daremus/tabletop_turn_timer/schematics/tabletop_game_timer_v1.kicad_sch

## KiCad design schematics/tabletop_game_timer_v1.kicad_sch (2026-09-04)

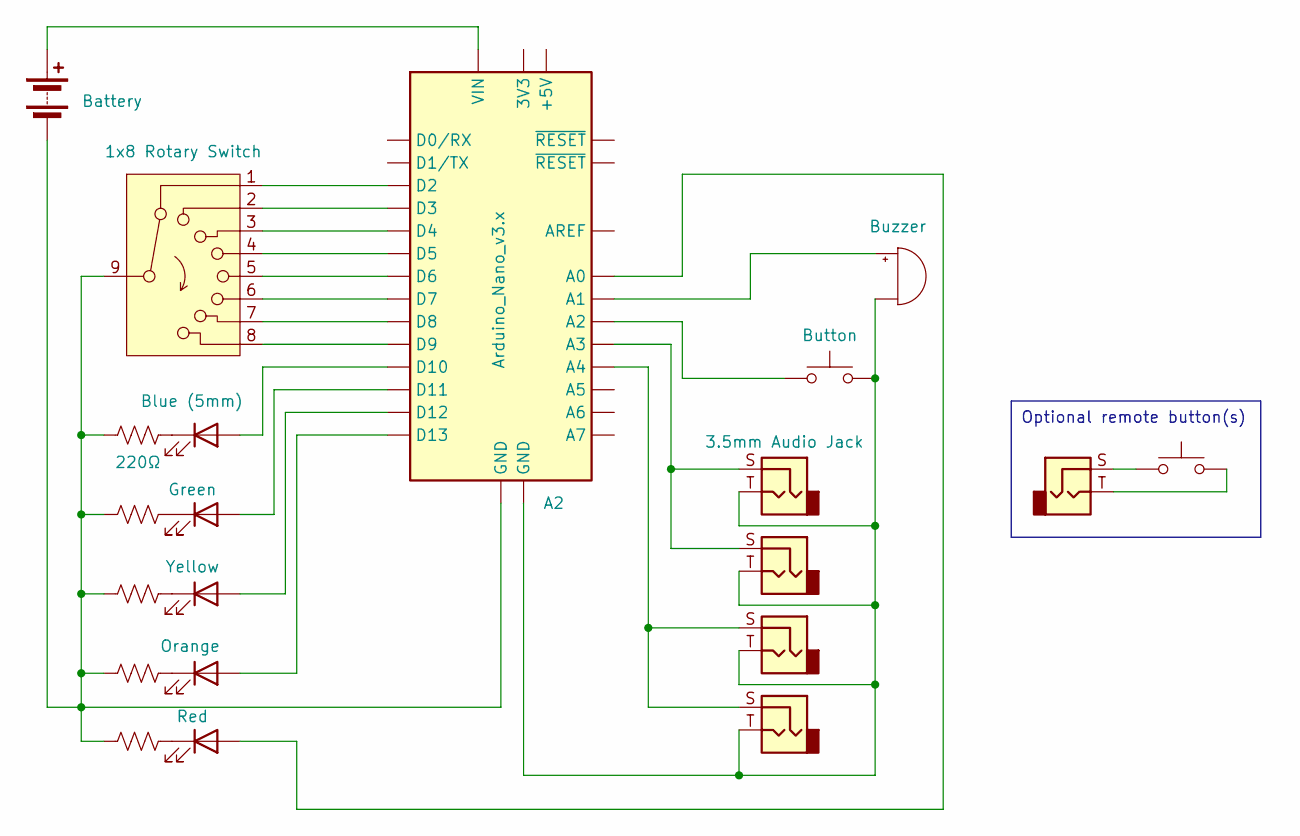
[picture p8: schematic tabletop_game_timer_v1.kicad_sch]

Parts:
220Ω, 220Ω1: R_US
A2: Arduino_Nano_v3.x; Arduino_Nano
BT1: Battery
BZ1: Buzzer
Blue: Blue (5mm)
Green: LED
J1, J2, J3, J4, J5: 3.5mm Audio Jack
Orange: LED
Red: LED
SW1: 1x8 Rotary Switch
SW2, SW3: Button
Yellow: LED

Connections:
unnamed: 220Ω1.2, Red.1 (K)
unnamed: 220Ω.1, 220Ω1.1, A2.4 (GND), BT1.2 (-), SW1.9
unnamed: 220Ω.2, Blue.1 (K), Green.1 (K), Orange.1 (K), Yellow.1 (K)
unnamed: A2.5 (D2), SW1.1
unnamed: A2.6 (D3), SW1.2
unnamed: A2.7 (D4), SW1.3
unnamed: A2.8 (D5), SW1.4
unnamed: A2.9 (D6), SW1.5
unnamed: A2.10 (D7), SW1.6
unnamed: A2.11 (D8), SW1.7
unnamed: A2.12 (D9), SW1.8
unnamed: A2.13 (D10), Blue.2 (A)
unnamed: A2.14 (D11), Green.2 (A)
unnamed: A2.15 (D12), Yellow.2 (A)
unnamed: A2.16 (D13), Orange.2 (A)
unnamed: A2.19 (A0), Red.2 (A)
unnamed: A2.20 (A1), BZ1.1 (+)
unnamed: A2.21 (A2), SW2.1
unnamed: A2.22 (A3), J1.S, J2.S
unnamed: A2.23 (A4), J3.S, J4.S
unnamed: A2.29 (GND), BZ1.2 (-), J1.T, J2.T, J3.T, J4.T, SW2.2
unnamed: A2.30 (VIN), BT1.1 (+)
unnamed: J5.S, SW3.1
unnamed: J5.T, SW3.2

Notes on the sheet:
Optional remote button(s)
